mrujzl/Hybrid_computer_v1/FW/core/max5437eud_reg_ctrl.h

/*
 * max5437eud_reg_ctrl.h
 *
 * Created: 16.10.2022
 *  Author: Miroslav Rujzl
 */ 


#ifndef MAX5437EUD_REG_CTRL_H_
#define MAX5437EUD_REG_CTRL_H_

// Registers


// Control
#define MAX5437EUD_MIN_RESISTANCE 	0x00
#define MAX5437EUD_HALF_RESISTANCE	0x3F
#define MAX5437EUD_MAX_RESISTANCE	0x7F


#endif /* MAX5437EUD_REG_CTRL_H_ */
